brianblong/CYD-Mini-TV/enclosure/prototype_v3/preview_housing.scad

// Fast view of the exported housing. Regenerate housing.stl after source edits.
import("housing.stl",convexity=30);
