brianblong/CYD-Mini-TV/firmware/include/server_roots.h

#pragma once

// Public Let's Encrypt trust anchors, fetched from the issuer on 2026-09-08.
// https://letsencrypt.org/certs/isrgrootx1.pem (expires 2035)
// https://letsencrypt.org/certs/isrg-root-x2.pem (expires 2040)
// Trust the issuing roots so normal Funnel leaf-certificate renewals keep working.
constexpr char kServerRootCertificates[] = R"PEM(-----BEGIN CERTIFICATE-----
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
-----END CERTIFICATE-----
-----BEGIN CERTIFICATE-----
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
/q4AaOeMSQ+2b1tbFfLn
-----END CERTIFICATE-----
)PEM";
